TheCaveCz/letsmake-wifilamp/firmware/lm-wifilamp/x02_log.ino

#if LOG_ENABLED
#define logRaw(msg) Serial.print(msg);
#else
#define logRaw(msg)
#endif

#define logLine() logRaw('\n')
#define logHeader() logRaw('[');logRaw(millis());logRaw("] ");
#define logInfo(msg) logHeader();logRaw(F(msg));logLine()
#define logValue(msg,val) logHeader();logRaw(F(msg));logRaw(val);logLine()
